TEK-Nemesis/Original-OGX360-Internal-Conversion-Kit/USB Breakout Boards/Motherboard 12-pin Extension/Images/12-pin_Extension.jpg

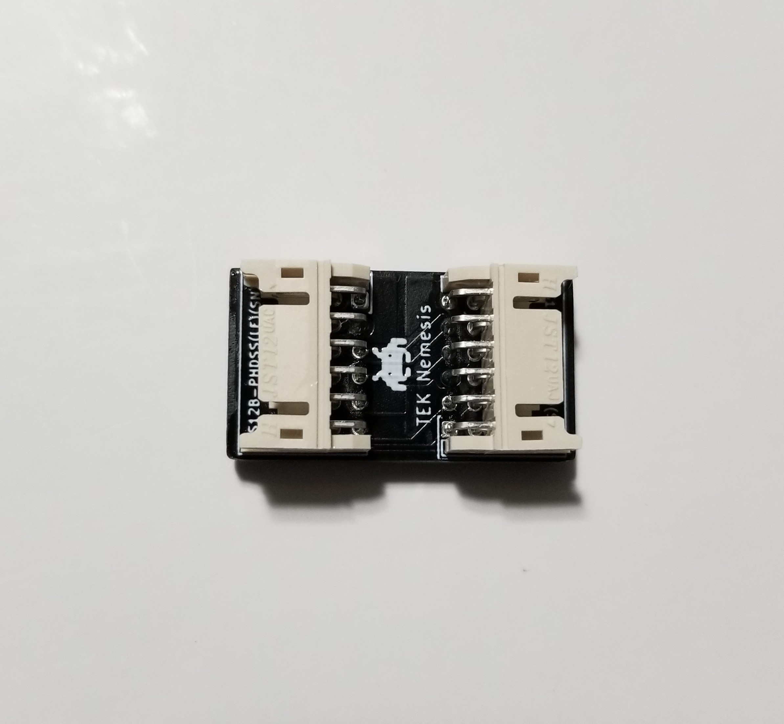
USB Breakout Boards/Motherboard 12-pin Extension/Images/12-pin_Extension.jpg
